J-Tech-Creations/Avocado55/design/scad/avocado55bodyBearing1.scad

include <avocado55.scad>;

bearingVersion = 1;
trackball55s(false,promicrohouse=false);
