J-Tech-Creations/Avocado55/design/scad/avocado55bottom.scad

include <avocado55.scad>;
trackball55s(true,promicrohouse=false);
