J-Tech-Creations/Avocado55/design/scad/cupBaseBearing1.scad

include <avocado55.scad>;

bearingVersion = 1;
cupBase(55,4,false,lift=13,small=true,bearing_shift=60,no_bearing=false);
